taborlab/LPA-hardware/docs/_images/culture_plate.png

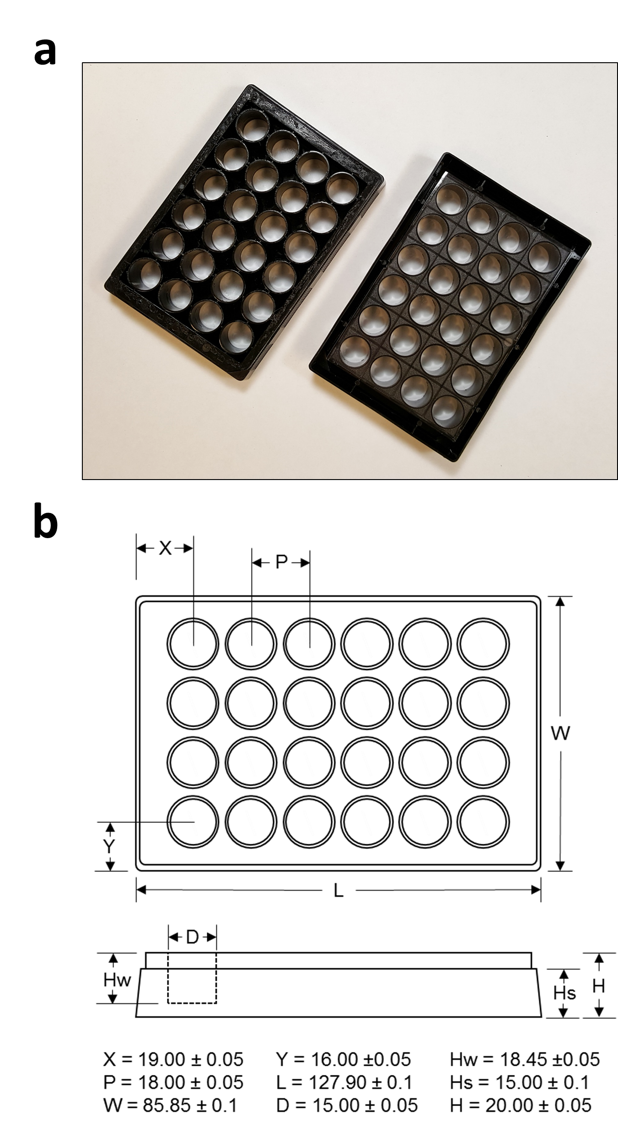
docs/_images/culture_plate.png
