taborlab/LPA-hardware/docs/_images/firmware_1.png

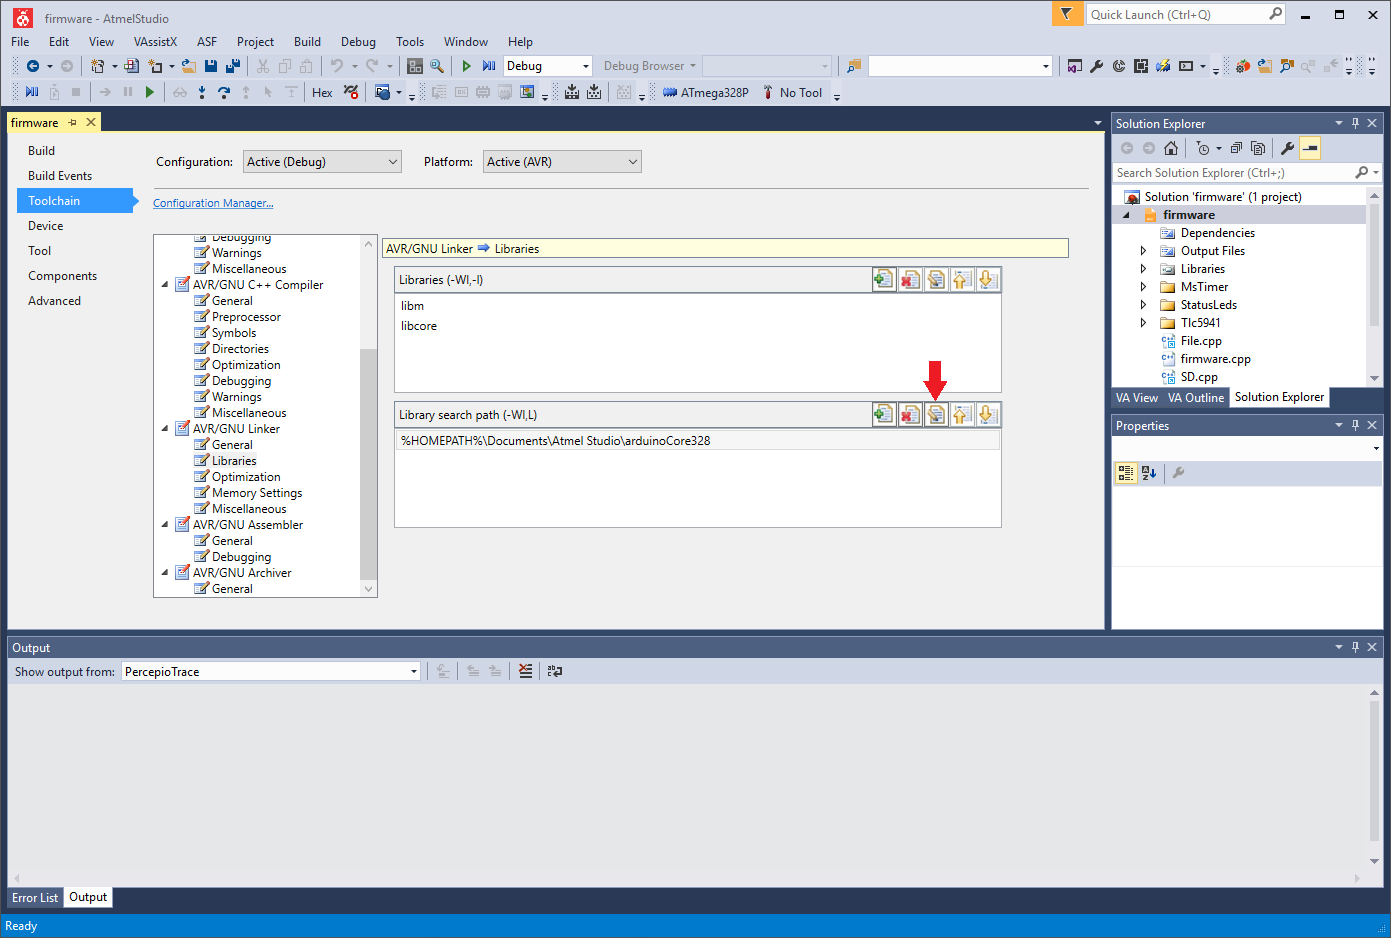
docs/_images/firmware_1.png
