taborlab/LPA-hardware/docs/_images/firmware_2.png

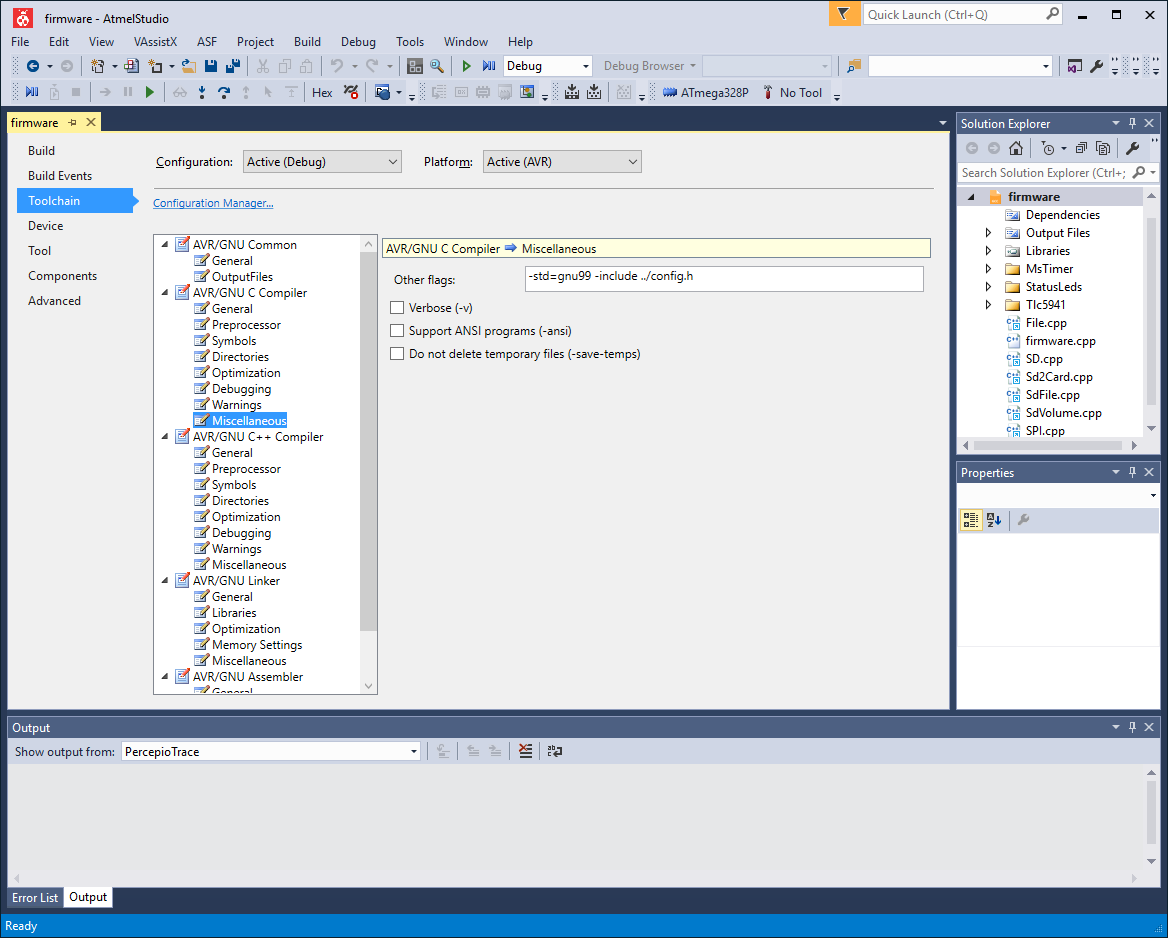
docs/_images/firmware_2.png
