taborlab/LPA-hardware/docs/_images/firmware_4.png

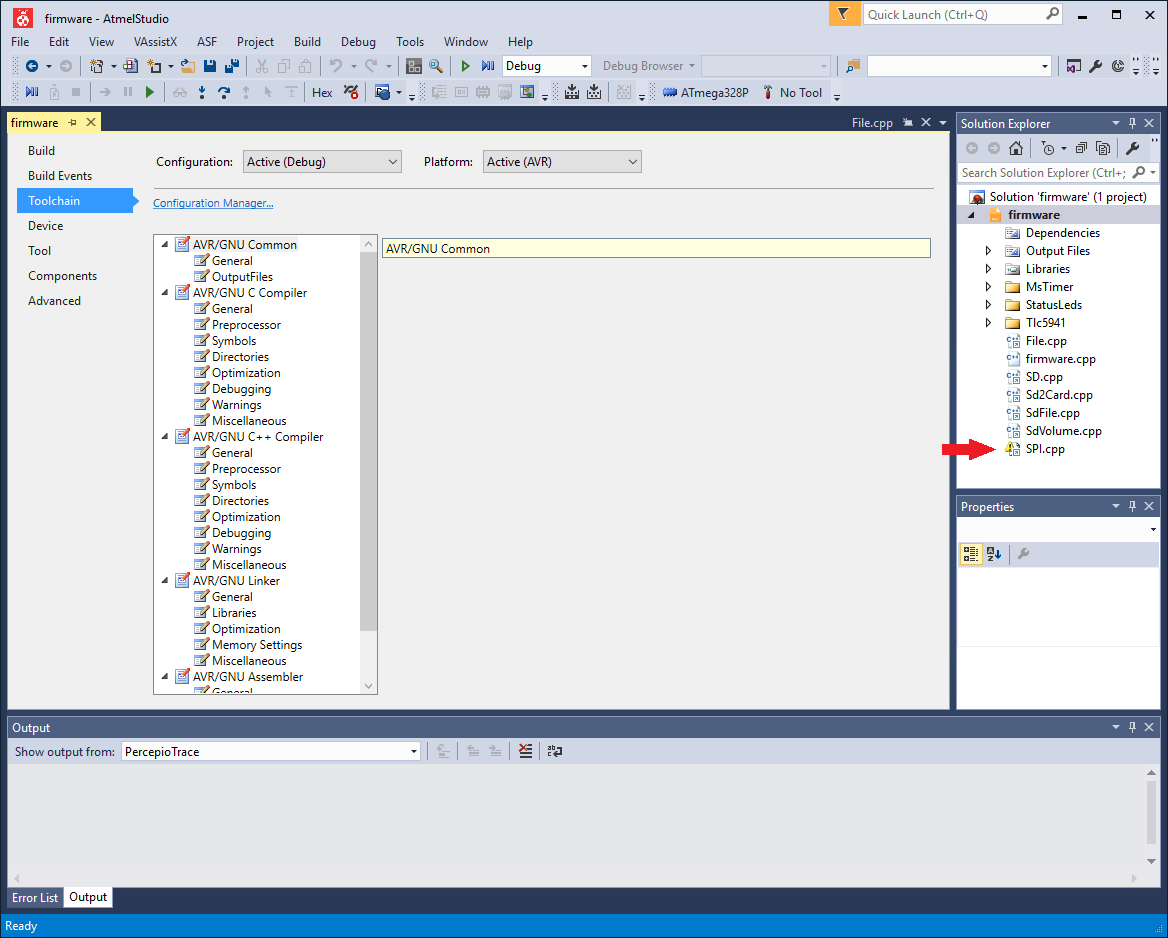
docs/_images/firmware_4.png
