taborlab/LPA-hardware/docs/_images/firmware_6.png

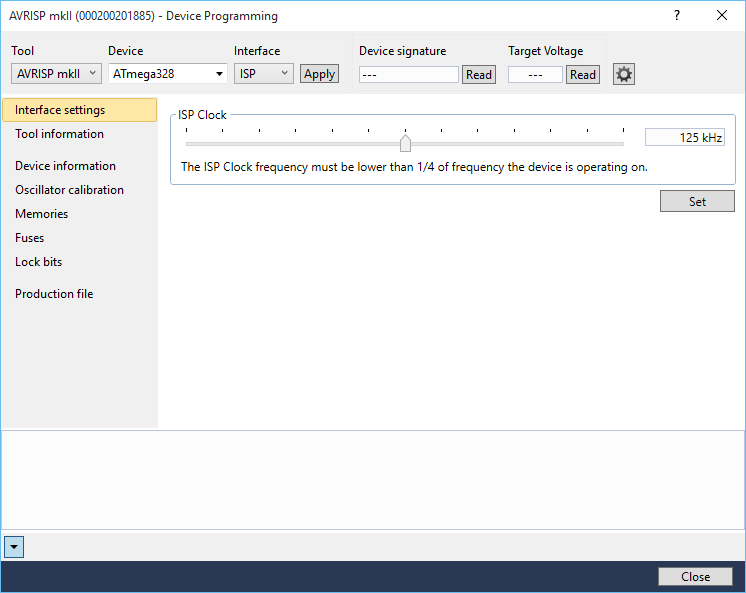
docs/_images/firmware_6.png
