taborlab/LPA-hardware/docs/_images/led_driver.png

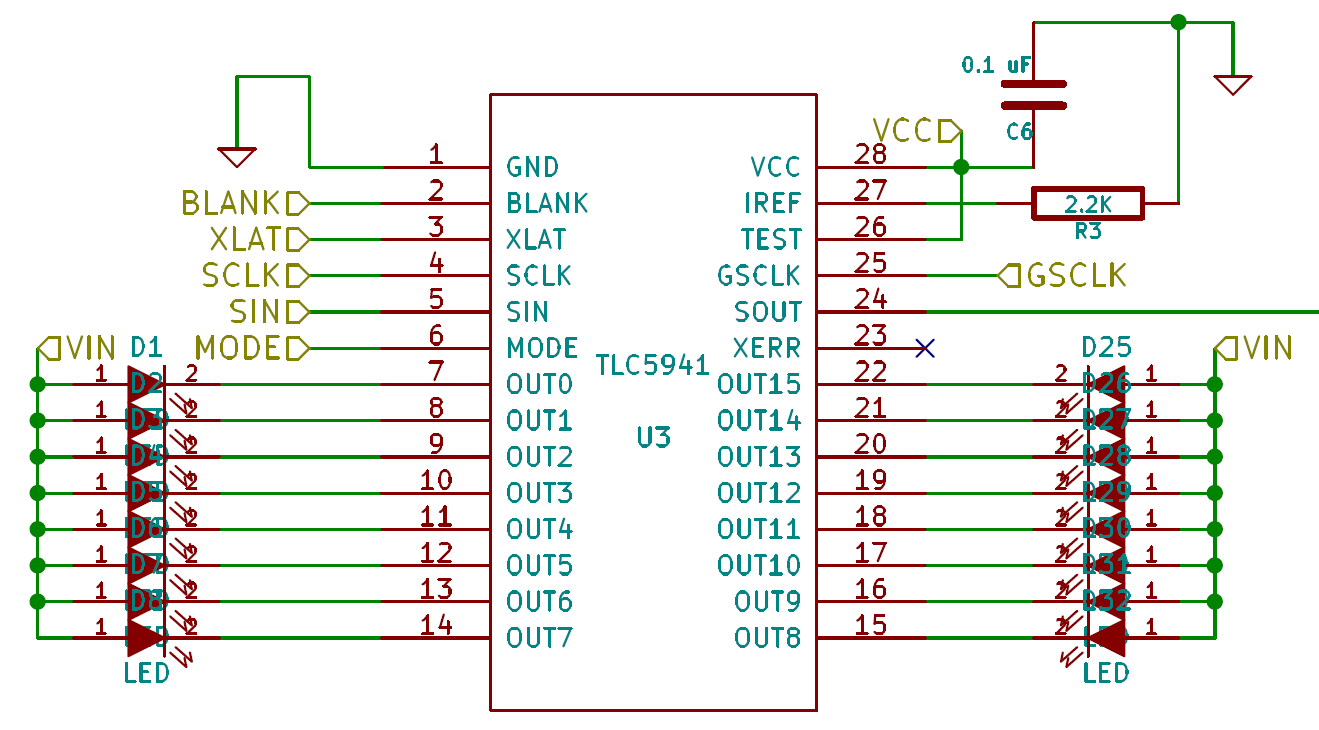
docs/_images/led_driver.png
