taborlab/LPA-hardware/docs/_images/led_socket.png

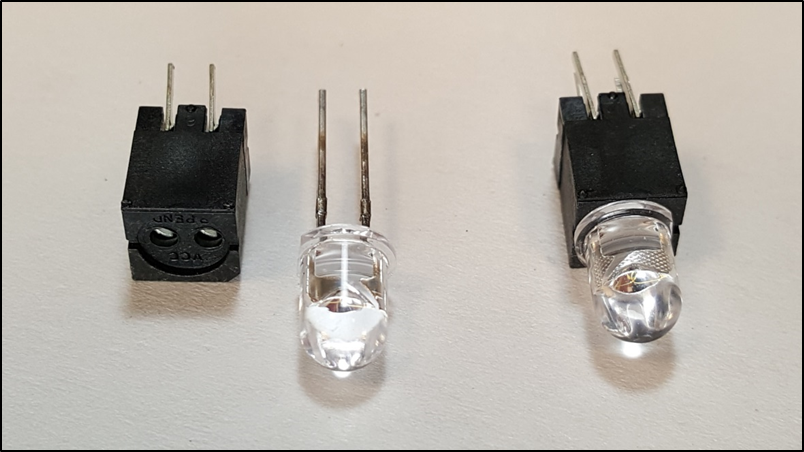
docs/_images/led_socket.png
