taborlab/LPA-hardware/docs/_images/pcb_labels.png

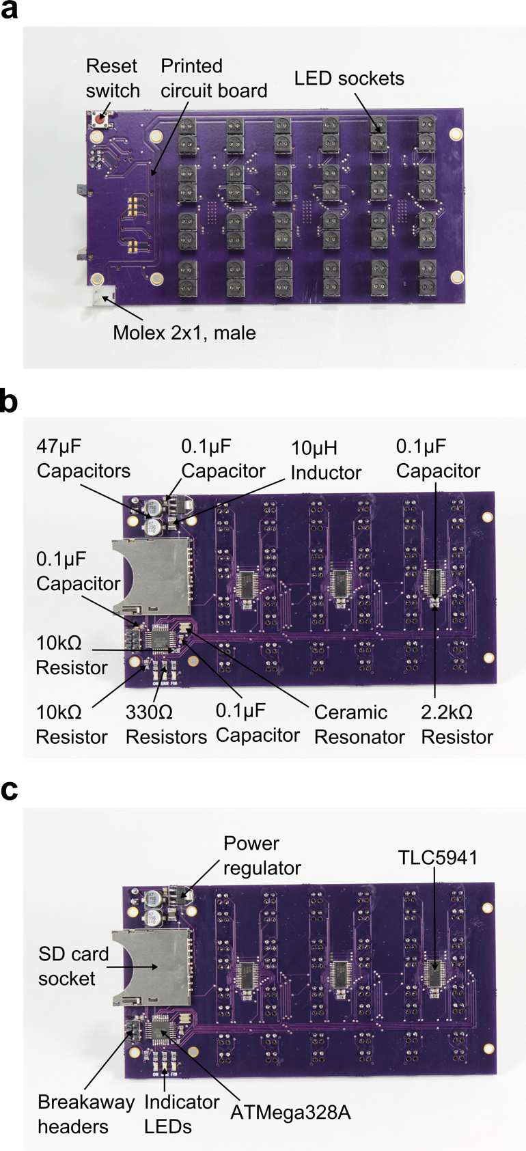
docs/_images/pcb_labels.png
