taborlab/LPA-hardware/docs/_images/power_connections.png

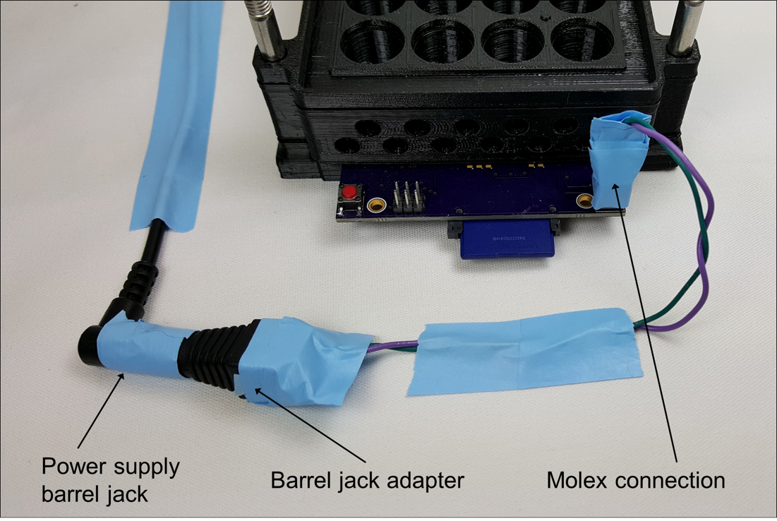
docs/_images/power_connections.png
