taborlab/LPA-hardware/docs/_images/sd_card.png

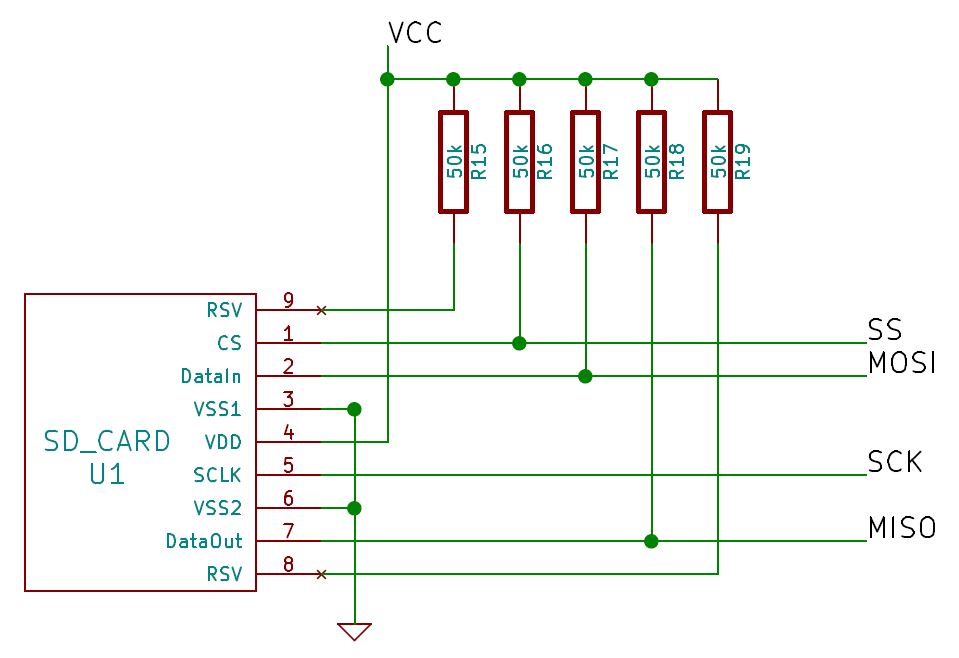
docs/_images/sd_card.png
