taborlab/LPA-hardware/Calibration/Image analysis script/example/arya_678nm_bot_150802/round1_T.tif

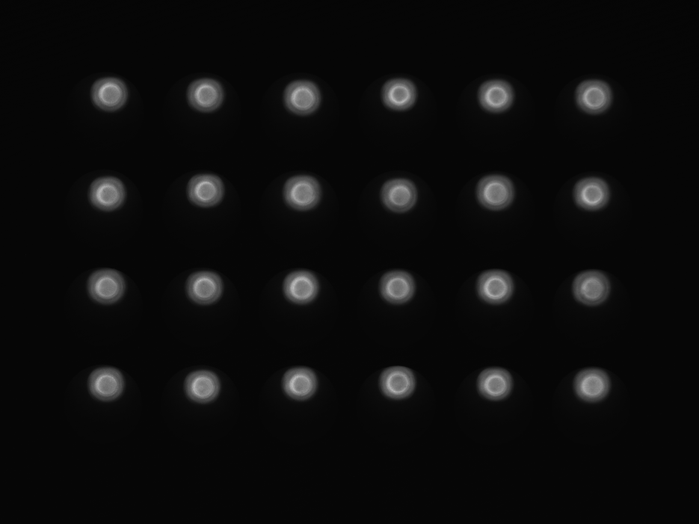
Calibration/Image analysis script/example/arya_678nm_bot_150802/round1_T.tif
